virtuosa0714/CASA0022-Bone-shaker-index/workload/kde.png

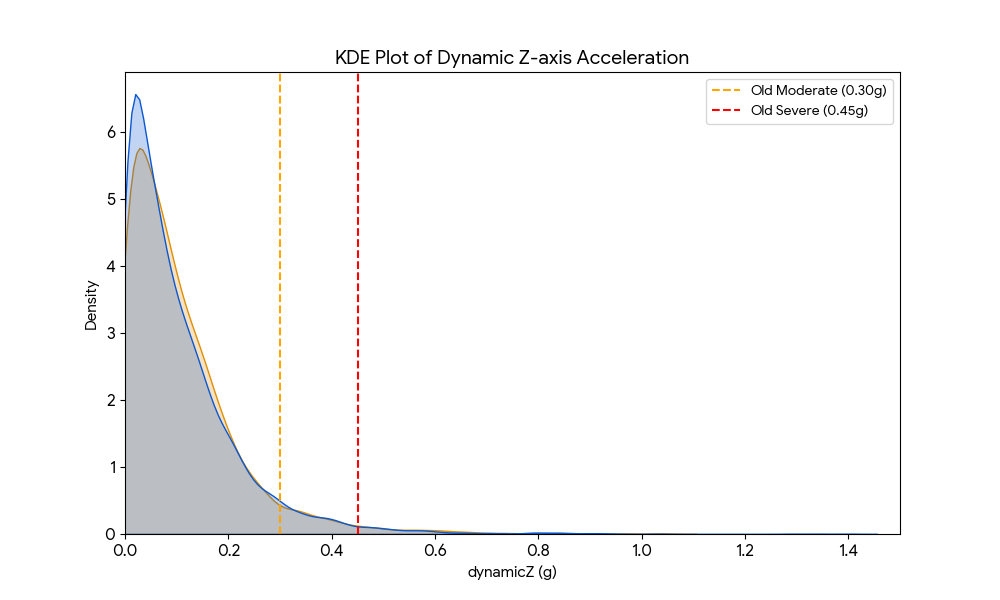
workload/kde.png
