virtuosa0714/CASA0022-Bone-shaker-index/workload/z_axis_analysis.png

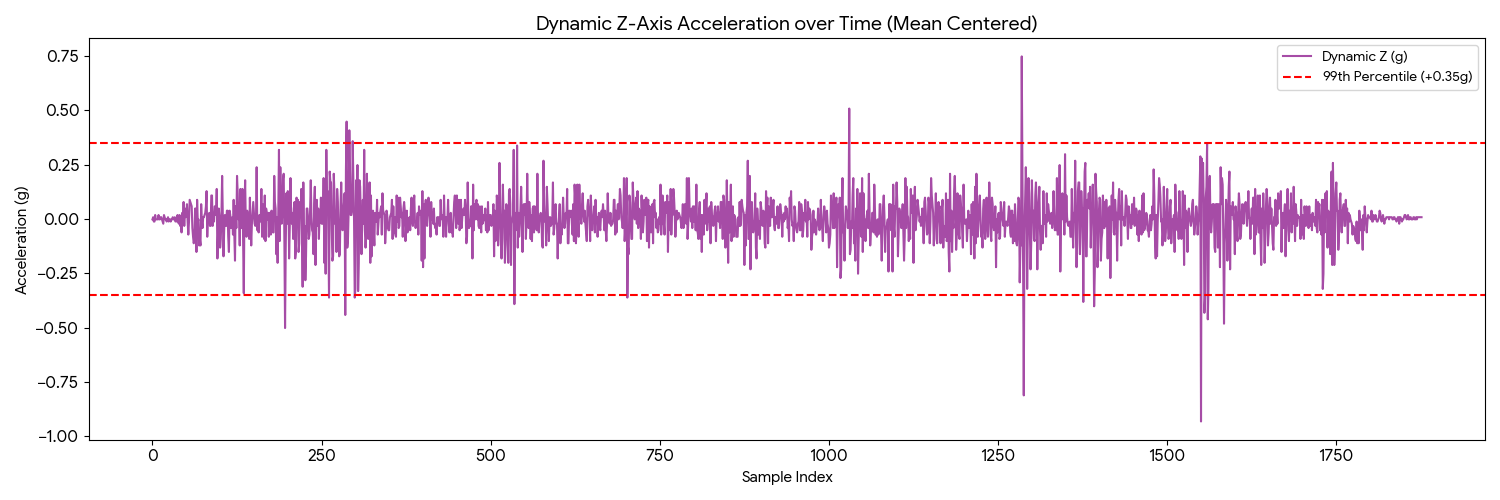
workload/z_axis_analysis.png
