virtuosa0714/CASA0022-Bone-shaker-index/workload/微信图片_20260512154936_144_30.jpg

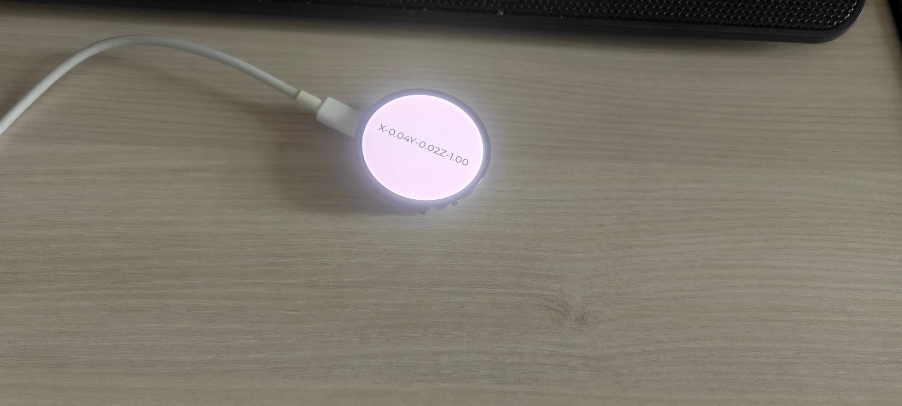
workload/微信图片_20260512154936_144_30.jpg
