virtuosa0714/CASA0022-Bone-shaker-index/workload/微信图片_20260520151158_161_30.jpg

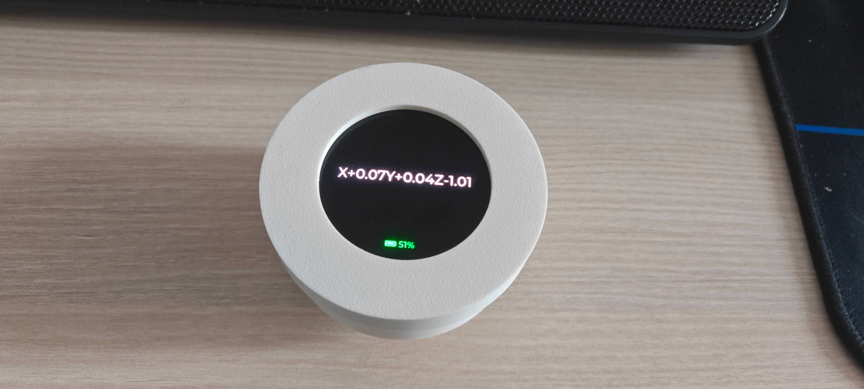
workload/微信图片_20260520151158_161_30.jpg
