virtuosa0714/CASA0022-Bone-shaker-index/workload/微信图片_20260602105240_178_30.jpg

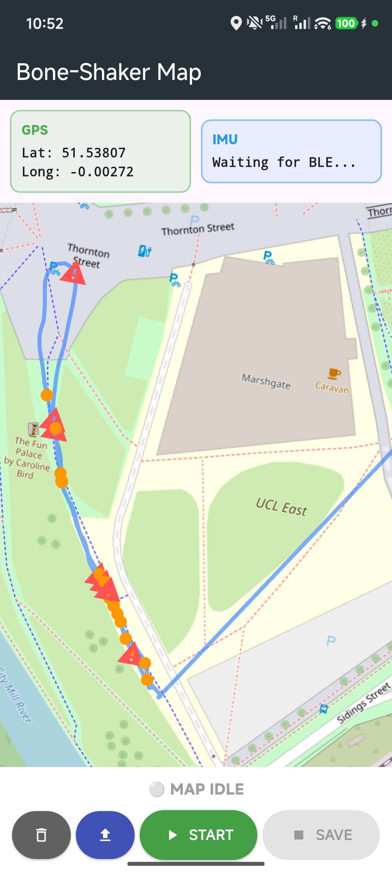
workload/微信图片_20260602105240_178_30.jpg
