virtuosa0714/CASA0022-Bone-shaker-index/workload/系统概念图.jpg

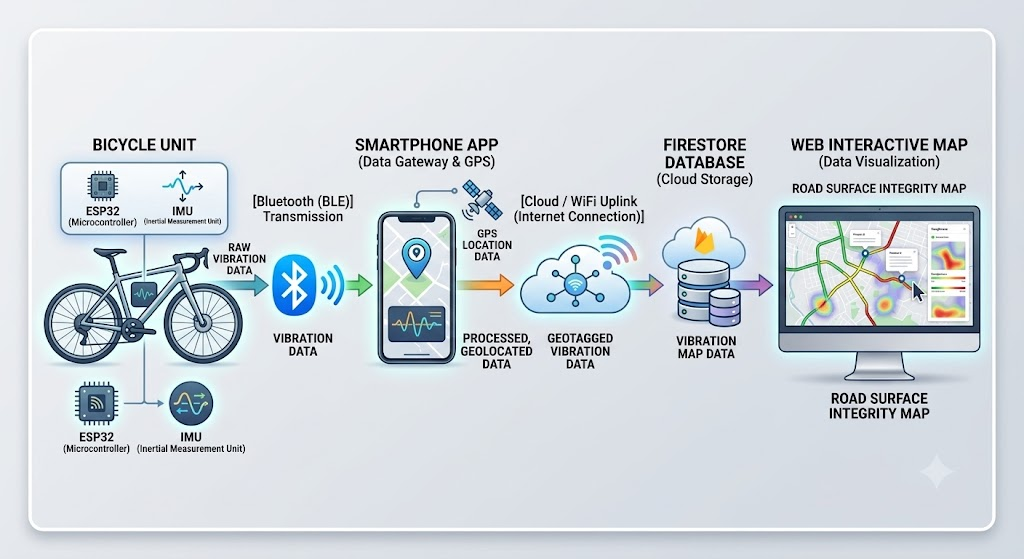
workload/系统概念图.jpg
